brad841/CAD-work/out/over_center_lever.step

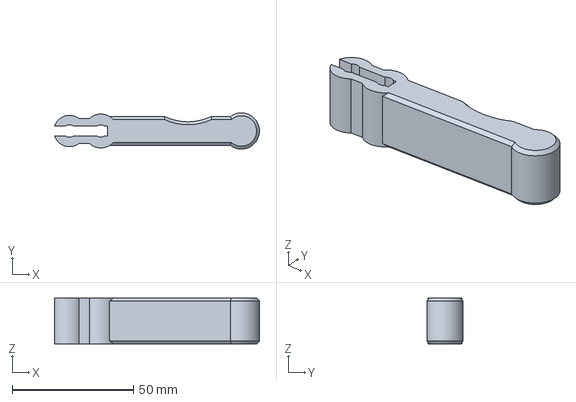
[picture p15: CAD file, 2026-08-05]
out/over_center_lever.step
84.7 x 15.0 x 19.0 mm
