brad841/CAD-work/out/bayonet_collar.step

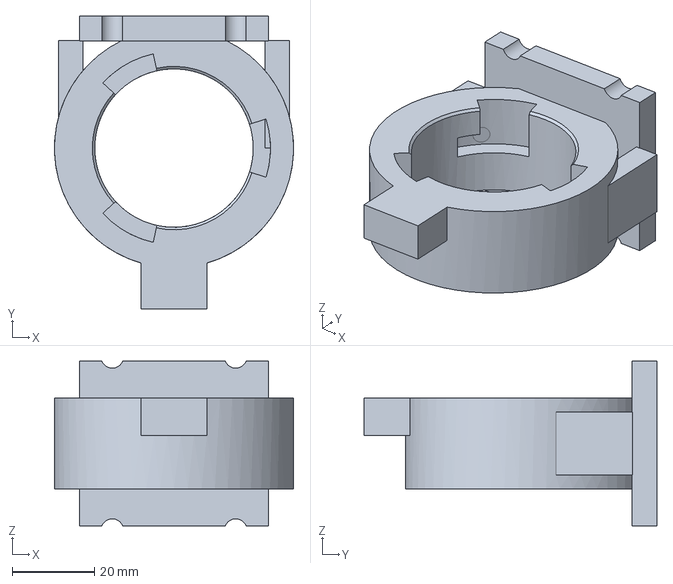
[picture p16: CAD file, 2026-08-05]
out/bayonet_collar.step
58.1 x 71.1 x 40.0 mm
