brad841/CAD-work/out/hook_nose.step

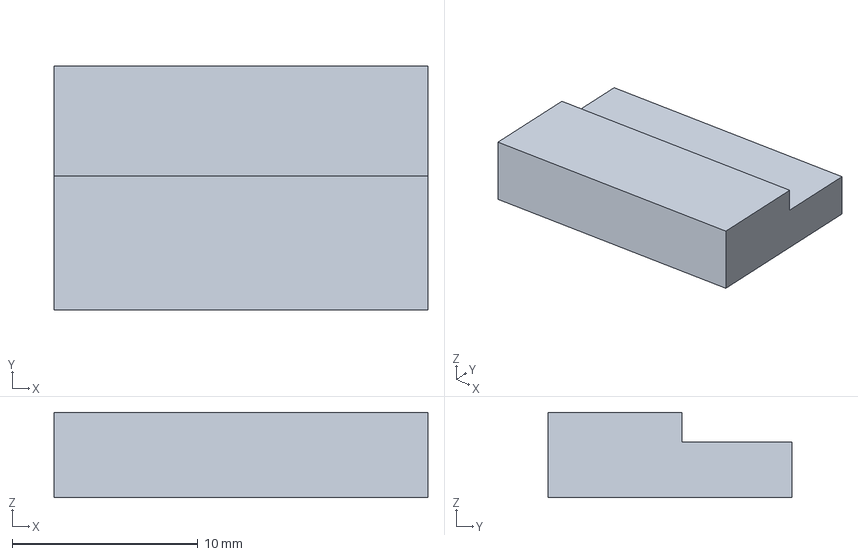
[picture p17: CAD file, 2026-08-05]
out/hook_nose.step
20.1 x 13.2 x 4.60 mm
