brad841/CAD-work/out/pole_shim_1p5mm.step

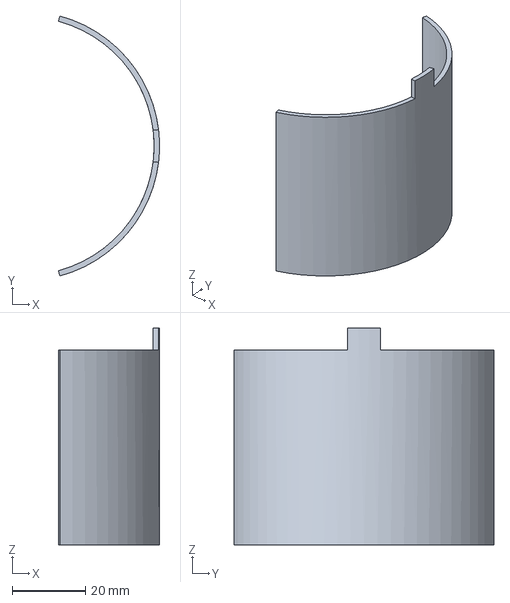
[picture p18: CAD file, 2026-08-05]
out/pole_shim_1p5mm.step
27.6 x 70.9 x 59.2 mm
