brad841/CAD-work/out/clamp_shell_swing.step

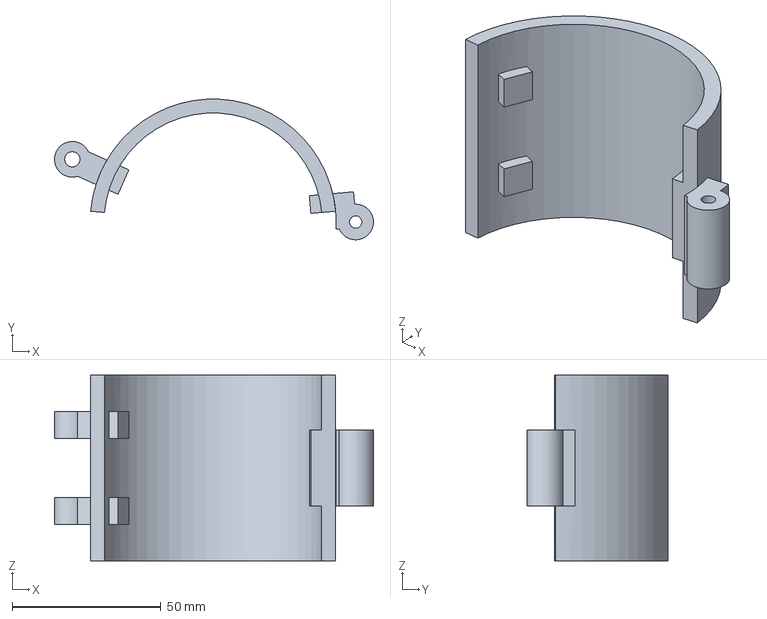
[picture p19: CAD file, 2026-08-05]
out/clamp_shell_swing.step
107.4 x 47.3 x 62.5 mm
